tgbugs/keyboard/LVC9-142399H-Rev.A_front.jpg

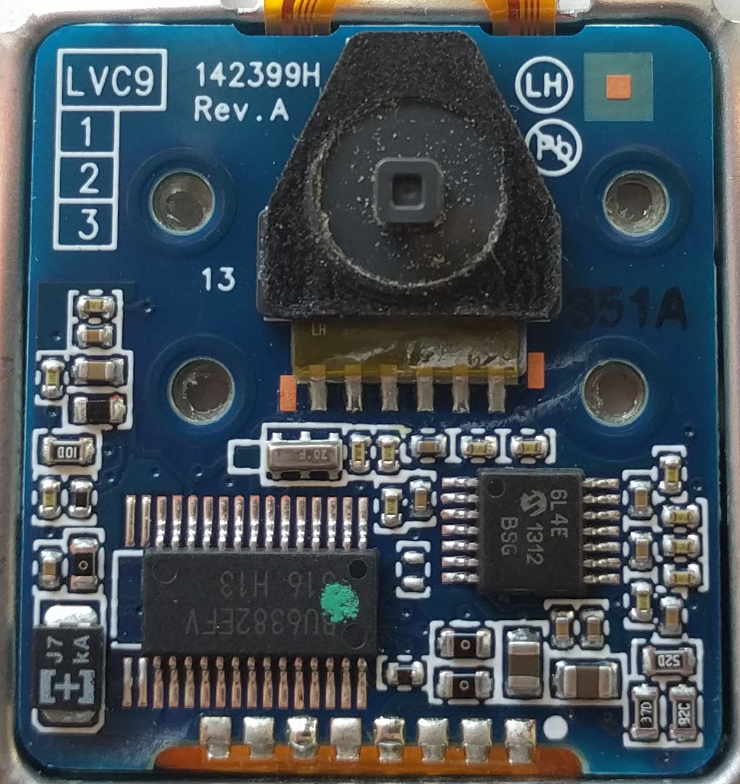
LVC9-142399H-Rev.A_front.jpg
